maks7d/FPVSoundLogger/PCB/3D/B3U-1000P.stp

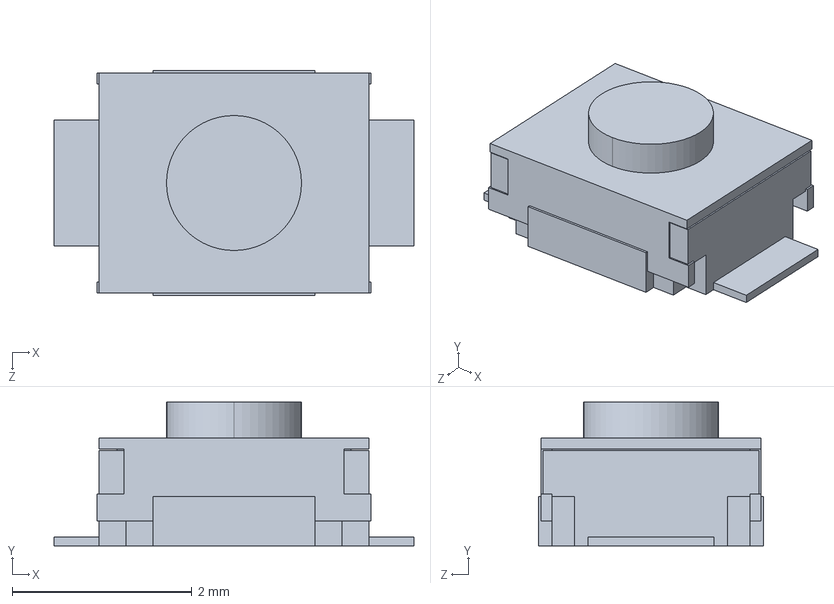
[picture p26: CAD file, 2025-12-18]
PCB/3D/B3U-1000P.stp
4.00 x 1.60 x 2.50 mm
