maks7d/FPVSoundLogger/PCB/3D/TLV75533PDBVR.step

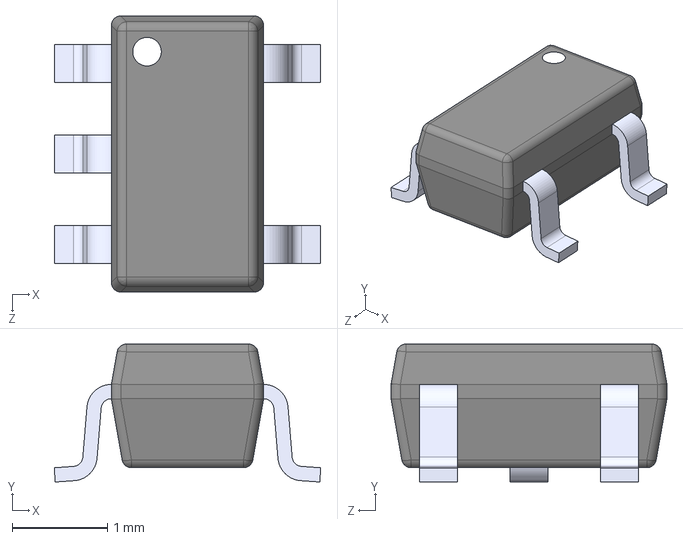
[picture p27: CAD file, 2026-04-24]
PCB/3D/TLV75533PDBVR.step
2.80 x 1.45 x 2.90 mm
