maks7d/FPVSoundLogger/PCB/3D/MAX40203AUK+T.stp

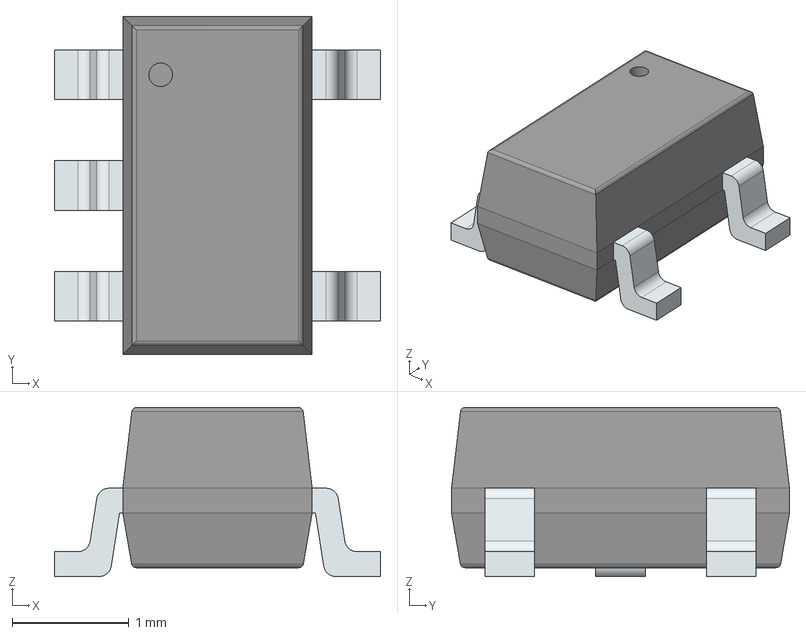
[picture p28: CAD file, 2026-04-24]
PCB/3D/MAX40203AUK+T.stp
2.80 x 2.90 x 1.45 mm
PinsArrayL
PinsArrayR
